Venta-Max/Venta-max-ventilator/Block_Diagram/Block diagram.jpeg

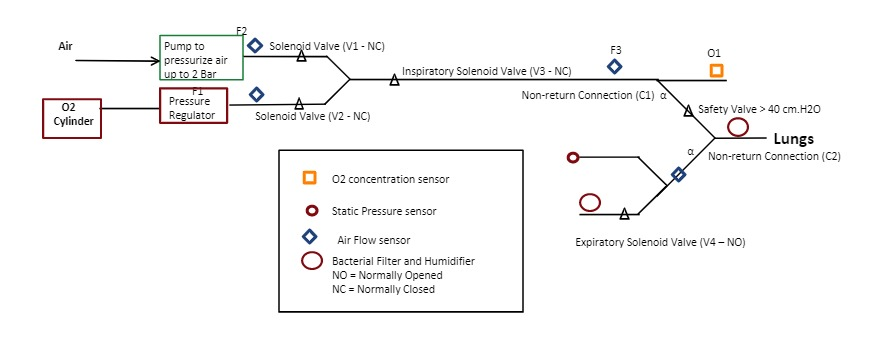
Block_Diagram/Block diagram.jpeg
