Venta-Max/Venta-max-ventilator/CAD Design/V1.1/Concept.jpg

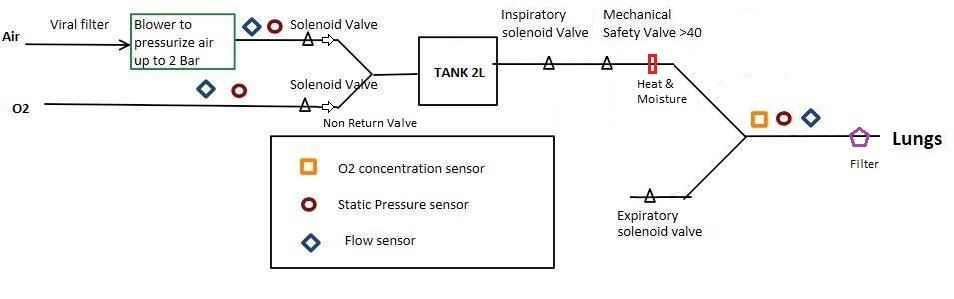
CAD Design/V1.1/Concept.jpg
