Venta-Max/Venta-max-ventilator/CAD Design/V1.1/Ventilator2.JPG

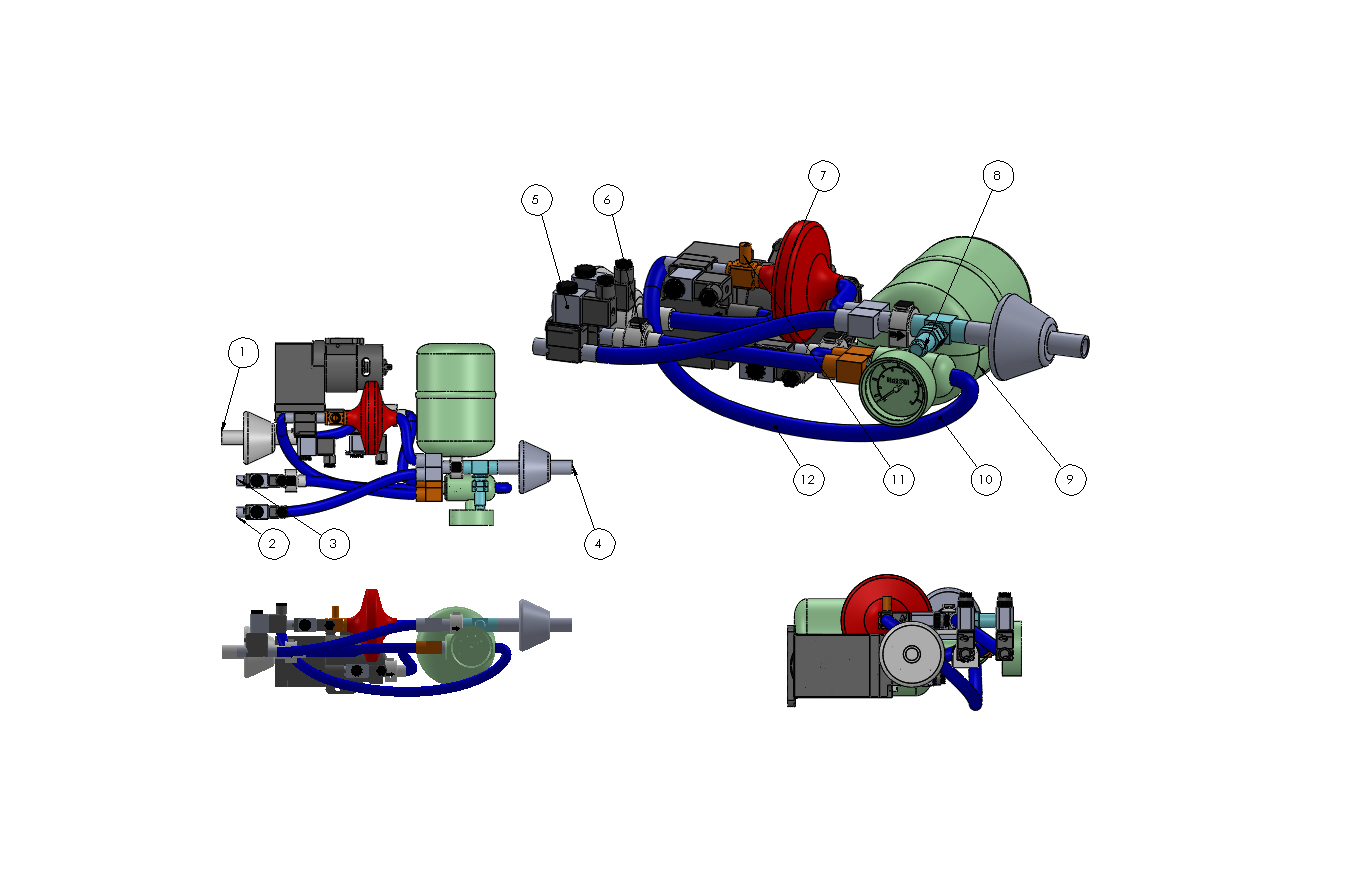
CAD Design/V1.1/Ventilator2.JPG
