Venta-Max/Venta-max-ventilator/CAD Design/V1.1/Selonoid.SLDPRT

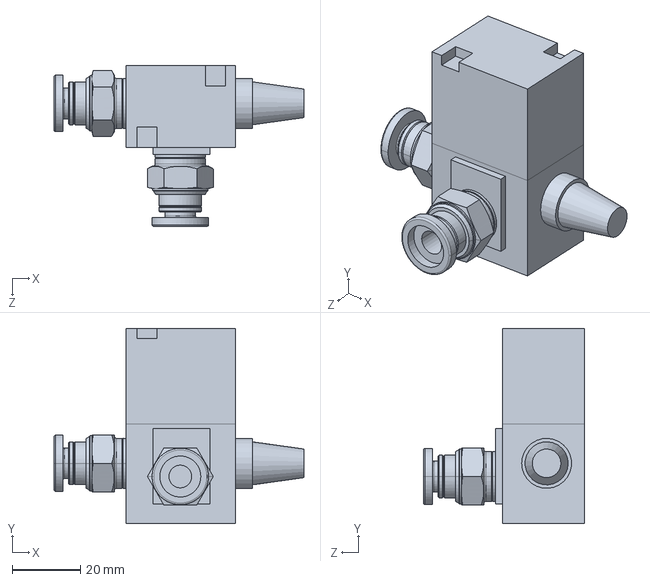
[picture p23: CAD file, 2020-04-27]
CAD Design/V1.1/Selonoid.SLDPRT
73.0 x 57.0 x 47.0 mm
