Venta-Max/Venta-max-ventilator/CAD Design/V1.1/Filter.SLDPRT

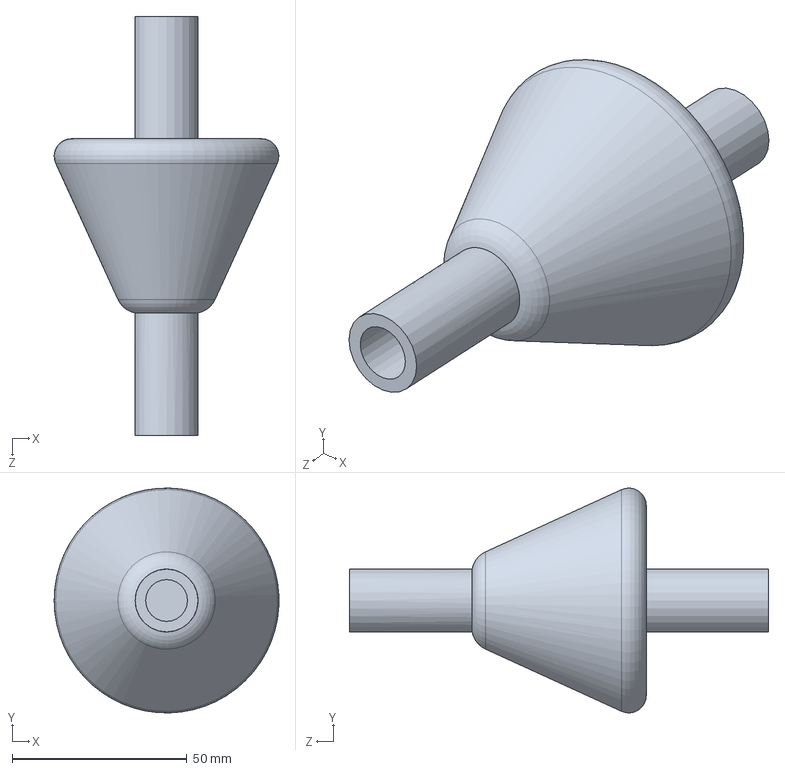
[picture p24: CAD file, 2020-04-27]
CAD Design/V1.1/Filter.SLDPRT
64.4 x 64.4 x 120.0 mm
