Venta-Max/Venta-max-ventilator/CAD Design/V1.1/Oxygen Sensor.SLDPRT

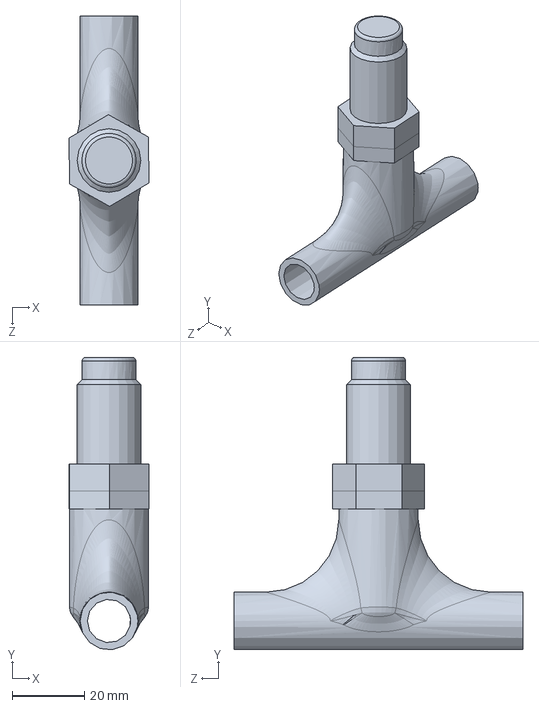
[picture p25: CAD file, 2020-04-27]
CAD Design/V1.1/Oxygen Sensor.SLDPRT
22.2 x 81.0 x 80.0 mm
