Venta-Max/Venta-max-ventilator/CAD Design/V1.1/Oneway Valve 3by8.SLDPRT

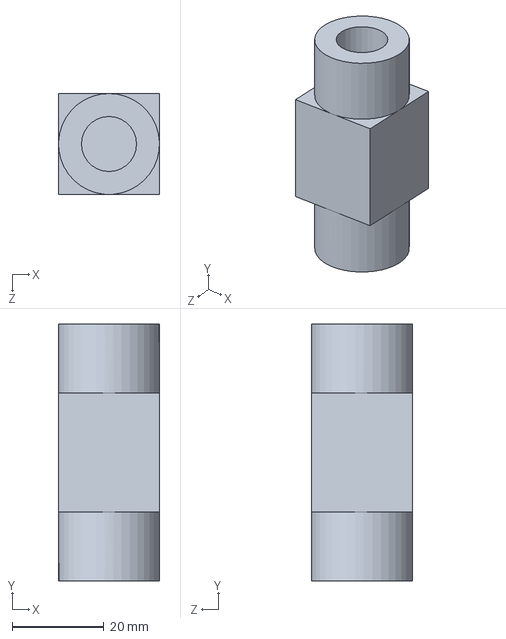
[picture p26: CAD file, 2020-04-27]
CAD Design/V1.1/Oneway Valve 3by8.SLDPRT
22.0 x 56.0 x 22.0 mm
