Venta-Max/Venta-max-ventilator/CAD Design/V1.1/O2 regulator.SLDPRT

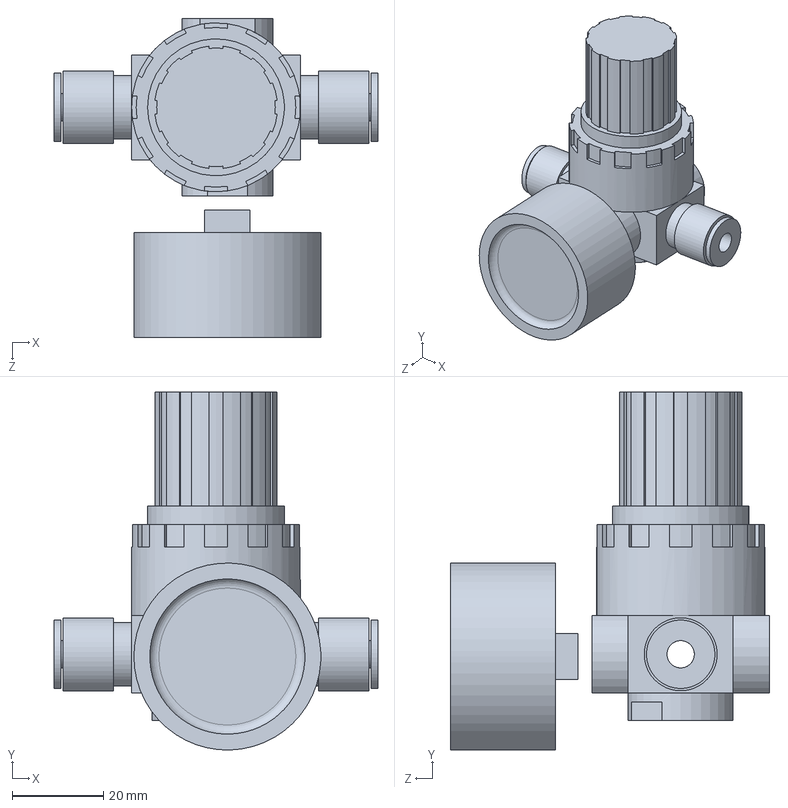
[picture p27: CAD file, 2020-04-27]
CAD Design/V1.1/O2 regulator.SLDPRT
71.0 x 78.5 x 70.0 mm
